linlun/HW-ESP8266_Roomba/Output/BoardCutoutAndSilkDescription.png

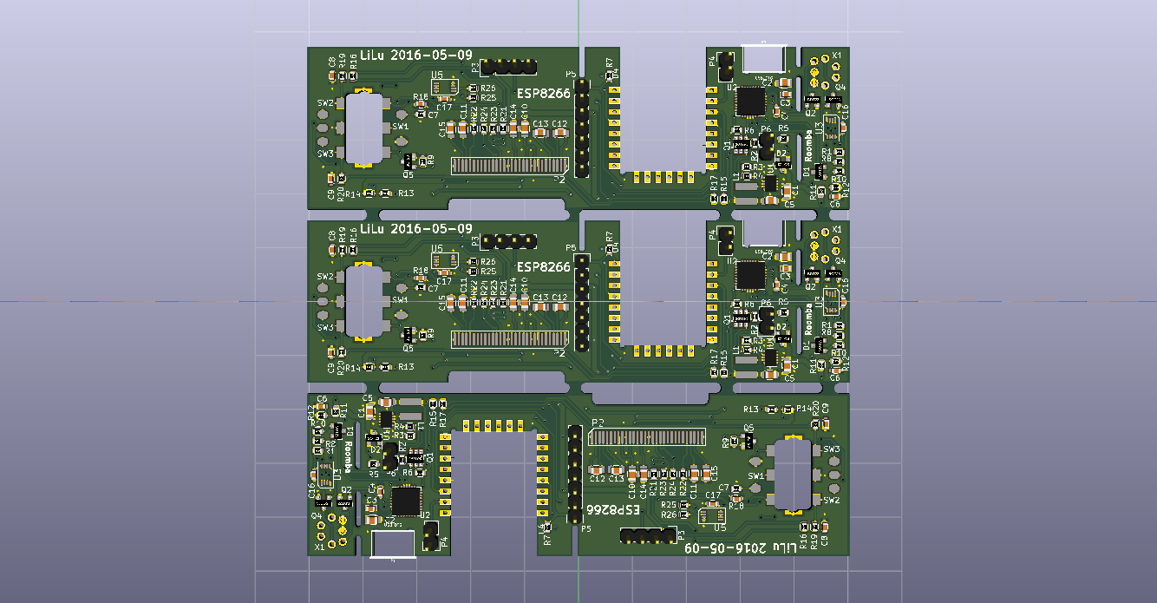
Output/BoardCutoutAndSilkDescription.png
